amorwilliams/Rools/firmware/src/board/cv_calibration.cpp

#include "board/cv_calibration.h"

namespace rools {

CvReferenceConfig CvCalToConfig(const CvCalibration& cal)
{
    const float gain = kCvAdcRefVolts / (cal.attenuation * kCvFullScaleVolts);
    return CvReferenceConfig{kCvAdcRefVolts, cal.center_volts, gain, true};
}

} // namespace rools
